akira215/zTank/drivers/include/flowMeter.h

/*
  zTank 
  Repository: https://github.com/akira215/
  License: GNU GENERAL PUBLIC LICENSE Version 3, 29 June 2007
  Author: Akira Shimahara
*/
#pragma once

#include "cppgpio.h"
#include "persistedValue.h"
#include "zbMeteringCluster.h"


#define GPIO_VOLUME_METER  CONFIG_VOLUME_METER_PIN  //!< GPIO number connect to the LED

/// @brief Driver to count volume from impulsion Meter - active low
class FlowMeter : public ZbMeteringCluster
{
    GpioInput _irqMeter { static_cast<gpio_num_t>(GPIO_VOLUME_METER) };
    PersistedValue<uint16_t> _Kfactor;
    uint32_t    _currentVolume = 0;

public:
    FlowMeter();
    int getPinLevel();

    /// @brief set the k factor of the volumetric meter (write to NVS)
    /// @param kFactor the factor (unit shall be the same as current volume)
    void setKfactor(uint16_t kFactor);

    /// @brief reset the Counter, after a reading for example
    void resetCounter();

    /// @brief get the volume counted from last reset
    /// @return the volume. Unit is the same as K factor
    uint32_t getCurrentVolume() const;

private:
    // Event Handler for cppButton
    static void impulsionHandler(void *handler_args, esp_event_base_t base,
                                 int32_t id, void *event_data);

};
